MakeOpenStuff/hestia32/docs/esp32-c5/dimensions.jpg

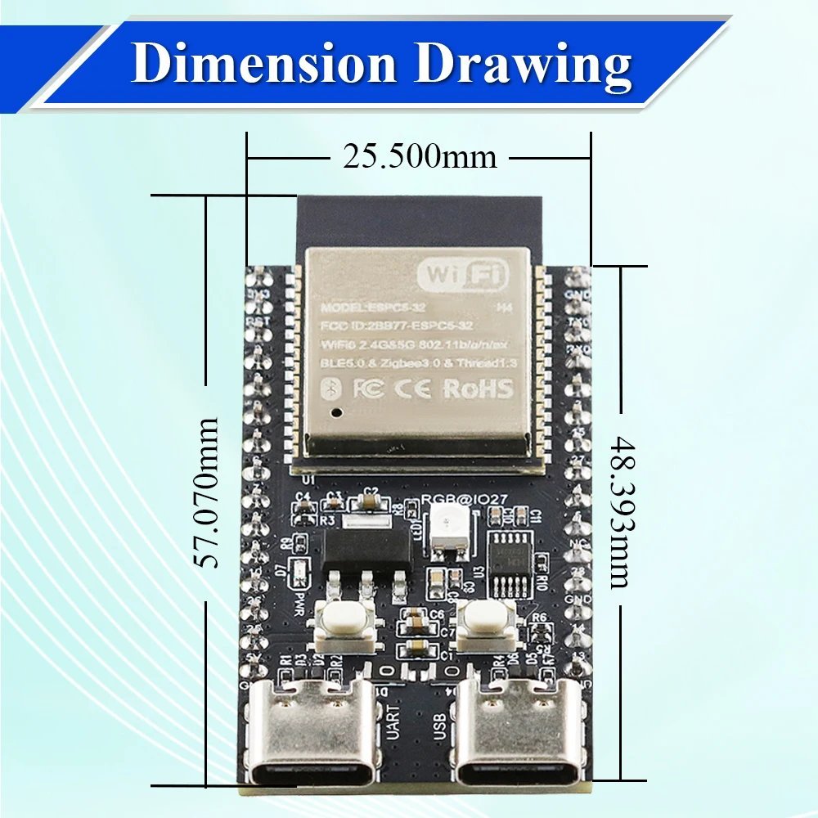
docs/esp32-c5/dimensions.jpg
