MakeOpenStuff/hestia32/docs/esp32-c5/photo1.jpg

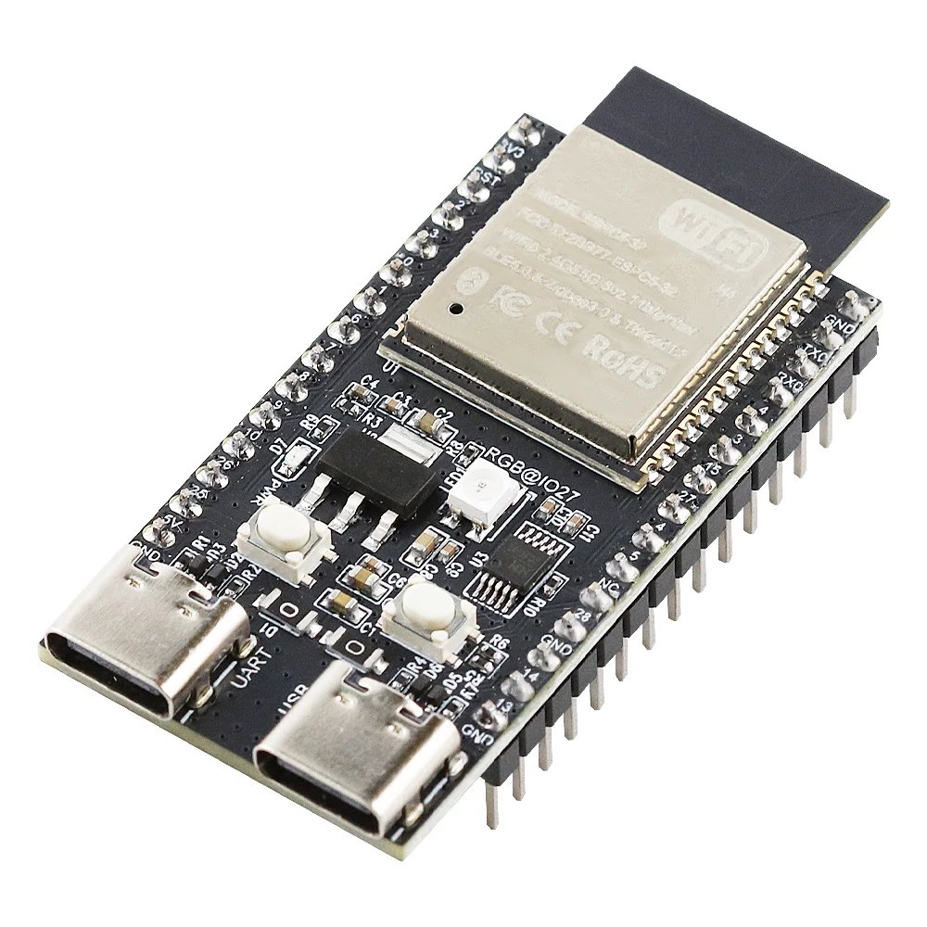
docs/esp32-c5/photo1.jpg
