MakeOpenStuff/hestia32/docs/esp32-c5/photo2.jpg

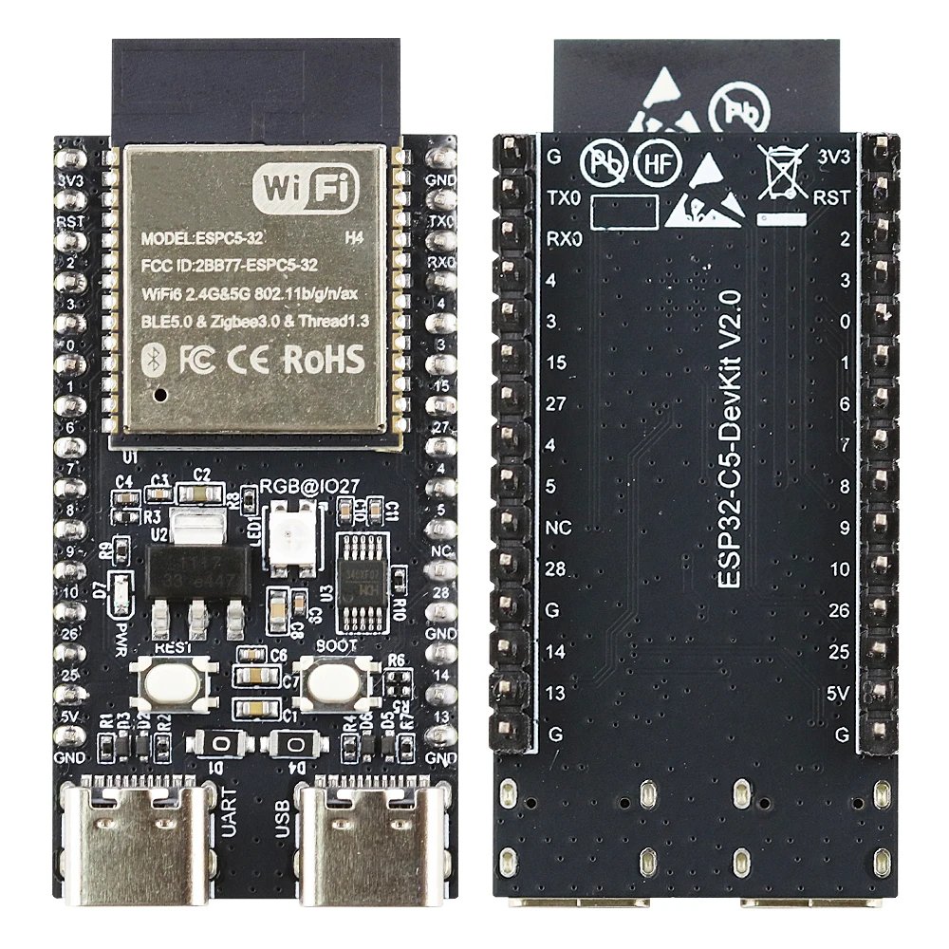
docs/esp32-c5/photo2.jpg
