MakeOpenStuff/hestia32/src/wifi_manager.c

#include "wifi_manager.h"
#include "config.h"

#include <string.h>
#include "freertos/FreeRTOS.h"
#include "freertos/task.h"
#include "freertos/event_groups.h"
#include "esp_system.h"
#include "esp_wifi.h"
#include "esp_event.h"
#include "esp_log.h"
#include "nvs_flash.h"

static const char *TAG = "wifi";
static EventGroupHandle_t wifi_event_group;
static int retry_count = 0;
static int max_retry_count = WIFI_MAX_RETRY;
static bool connected = false;

#define WIFI_CONNECTED_BIT BIT0
#define WIFI_FAIL_BIT      BIT1

static void event_handler(void* arg, esp_event_base_t event_base,
                         int32_t event_id, void* event_data)
{
    if (event_base == WIFI_EVENT && event_id == WIFI_EVENT_STA_START) {
        esp_wifi_connect();
    } else if (event_base == WIFI_EVENT && event_id == WIFI_EVENT_STA_DISCONNECTED) {
        if (retry_count < max_retry_count) {
            esp_wifi_connect();
            retry_count++;
            ESP_LOGI(TAG, "Retrying to connect to AP... (%d/%d)", retry_count, max_retry_count);
        } else {
            xEventGroupSetBits(wifi_event_group, WIFI_FAIL_BIT);
            ESP_LOGI(TAG, "Failed to connect to AP");
        }
        connected = false;
    } else if (event_base == IP_EVENT && event_id == IP_EVENT_STA_GOT_IP) {
        ip_event_got_ip_t* event = (ip_event_got_ip_t*) event_data;
        ESP_LOGI(TAG, "Got IP: " IPSTR, IP2STR(&event->ip_info.ip));
        retry_count = 0;
        connected = true;
        xEventGroupSetBits(wifi_event_group, WIFI_CONNECTED_BIT);
    }
}

esp_err_t wifi_init(void)
{
    esp_err_t ret = nvs_flash_init();
    if (ret == ESP_ERR_NVS_NO_FREE_PAGES || ret == ESP_ERR_NVS_NEW_VERSION_FOUND) {
        ESP_ERROR_CHECK(nvs_flash_erase());
        ret = nvs_flash_init();
    }
    ESP_ERROR_CHECK(ret);

    wifi_event_group = xEventGroupCreate();

    // Check if netif is already initialized (might be done by provisioning)
    ret = esp_netif_init();
    if (ret != ESP_OK && ret != ESP_ERR_INVALID_STATE) {
        ESP_ERROR_CHECK(ret);
    }

    // Check if event loop is already created (might be done by provisioning)
    ret = esp_event_loop_create_default();
    if (ret != ESP_OK && ret != ESP_ERR_INVALID_STATE) {
        ESP_ERROR_CHECK(ret);
    }

    // Check if WiFi STA interface already exists (might be created by provisioning)
    esp_netif_t* sta_netif = esp_netif_get_handle_from_ifkey("WIFI_STA_DEF");
    if (sta_netif == NULL) {
        esp_netif_create_default_wifi_sta();
    }

    wifi_init_config_t cfg = WIFI_INIT_CONFIG_DEFAULT();
    ret = esp_wifi_init(&cfg);
    if (ret != ESP_OK && ret != ESP_ERR_INVALID_STATE) {
        ESP_ERROR_CHECK(ret);
    }

    esp_event_handler_instance_t instance_any_id;
    esp_event_handler_instance_t instance_got_ip;

    ESP_ERROR_CHECK(esp_event_handler_instance_register(WIFI_EVENT,
                                                        ESP_EVENT_ANY_ID,
                                                        &event_handler,
                                                        NULL,
                                                        &instance_any_id));
    ESP_ERROR_CHECK(esp_event_handler_instance_register(IP_EVENT,
                                                        IP_EVENT_STA_GOT_IP,
                                                        &event_handler,
                                                        NULL,
                                                        &instance_got_ip));

    ESP_ERROR_CHECK(esp_wifi_set_mode(WIFI_MODE_STA));

    ESP_LOGI(TAG, "WiFi initialized");
    return ESP_OK;
}

esp_err_t wifi_connect(const char *ssid, const char *password, int max_retry)
{
    max_retry_count = max_retry;
    retry_count = 0;

    wifi_config_t wifi_config = {
        .sta = {
            .threshold.authmode = WIFI_AUTH_WPA2_PSK,
            .pmf_cfg = {
                .capable = true,
                .required = false
            },
        },
    };

    strncpy((char *)wifi_config.sta.ssid, ssid, sizeof(wifi_config.sta.ssid) - 1);
    strncpy((char *)wifi_config.sta.password, password, sizeof(wifi_config.sta.password) - 1);

    ESP_ERROR_CHECK(esp_wifi_set_config(WIFI_IF_STA, &wifi_config));
    ESP_ERROR_CHECK(esp_wifi_start());

    ESP_LOGI(TAG, "Connecting to WiFi SSID: %s", ssid);

    EventBits_t bits = xEventGroupWaitBits(wifi_event_group,
            WIFI_CONNECTED_BIT | WIFI_FAIL_BIT,
            pdFALSE,
            pdFALSE,
            portMAX_DELAY);

    if (bits & WIFI_CONNECTED_BIT) {
        ESP_LOGI(TAG, "Connected to AP");
        return ESP_OK;
    } else if (bits & WIFI_FAIL_BIT) {
        ESP_LOGI(TAG, "Failed to connect to AP");
        return ESP_FAIL;
    } else {
        ESP_LOGE(TAG, "Unexpected event");
        return ESP_FAIL;
    }
}

void wifi_disconnect(void)
{
    esp_wifi_disconnect();
    esp_wifi_stop();
    connected = false;
    ESP_LOGI(TAG, "WiFi disconnected");
}

bool wifi_is_connected(void)
{
    return connected;
}
